Nikorag/Jellybox-Firmware/jellybox-firmware/JellyboxLogo.h

// Jellybox logo — 72x72 px, 9 bytes/row
static const uint8_t JELLYBOX_LOGO[] PROGMEM = {
  0x00, 0x00, 0x00, 0x00, 0x00, 0x00, 0x00, 0x00, 0x00,
  0x00, 0x00, 0x00, 0x00, 0x00, 0x00, 0x00, 0x00, 0x00,
  0x00, 0x00, 0x00, 0x00, 0x00, 0x00, 0x00, 0x00, 0x00,
  0x00, 0x00, 0x00, 0x00, 0x00, 0x00, 0x00, 0x00, 0x00,
  0x00, 0x00, 0x00, 0x00, 0x00, 0x00, 0x00, 0x00, 0x00,
  0x00, 0x00, 0x00, 0x00, 0x00, 0x00, 0x00, 0x00, 0x00,
  0x00, 0x00, 0x00, 0x00, 0x00, 0x00, 0x00, 0x00, 0x00,
  0x00, 0x00, 0x00, 0x00, 0x00, 0x00, 0x00, 0x00, 0x00,
  0x00, 0x00, 0x00, 0x00, 0x00, 0x00, 0x00, 0x00, 0x00,
  0x00, 0x00, 0x00, 0x00, 0x00, 0x00, 0x00, 0x00, 0x00,
  0x00, 0x00, 0x00, 0x00, 0x00, 0x00, 0x00, 0x00, 0x00,
  0x00, 0x00, 0x00, 0x00, 0x00, 0x00, 0x00, 0x00, 0x00,
  0x00, 0x00, 0x00, 0x00, 0x00, 0x00, 0x00, 0x00, 0x00,
  0x00, 0x00, 0x00, 0x00, 0x00, 0x00, 0x00, 0x00, 0x00,
  0x00, 0x00, 0x00, 0x00, 0x00, 0x00, 0x00, 0x00, 0x00,
  0x00, 0x00, 0x00, 0x00, 0xFF, 0x00, 0x00, 0x00, 0x00,
  0x00, 0x00, 0x00, 0x3F, 0xFF, 0xFC, 0x00, 0x00, 0x00,
  0x00, 0x00, 0x00, 0x63, 0xFF, 0xC6, 0x00, 0x00, 0x00,
  0x00, 0x00, 0x00, 0xC3, 0xFF, 0xC3, 0x00, 0x00, 0x00,
  0x00, 0x00, 0x01, 0x9C, 0x3C, 0x39, 0x80, 0x00, 0x00,
  0x00, 0x00, 0x01, 0x38, 0x7E, 0x1C, 0x80, 0x00, 0x00,
  0x00, 0x00, 0x03, 0x31, 0xC3, 0x8C, 0xC0, 0x00, 0x00,
  0x00, 0x00, 0x02, 0x73, 0x81, 0xCE, 0x40, 0x00, 0x00,
  0x00, 0x00, 0x02, 0x67, 0x9E, 0xE6, 0x40, 0x00, 0x00,
  0x00, 0x00, 0x06, 0xE7, 0x3F, 0xE7, 0x60, 0x00, 0x00,
  0x00, 0x00, 0xFC, 0xE7, 0x3F, 0xE7, 0x3F, 0x00, 0x00,
  0x00, 0x03, 0xED, 0xCF, 0x3F, 0xF7, 0xB7, 0xC0, 0x00,
  0x00, 0x07, 0x0D, 0xCF, 0xFF, 0xF3, 0xB0, 0xE0, 0x00,
  0x00, 0x0F, 0xC9, 0xCF, 0xFF, 0xF3, 0x93, 0xF0, 0x00,
  0x00, 0x0C, 0x79, 0xDF, 0x7F, 0xFB, 0x9E, 0x30, 0x00,
  0x00, 0x18, 0x3F, 0xDF, 0xFF, 0xFB, 0xF8, 0x18, 0x00,
  0x00, 0x18, 0x0F, 0x9F, 0xFF, 0xF9, 0xF0, 0x18, 0x00,
  0x00, 0x30, 0x03, 0xFF, 0xFF, 0xFF, 0xC0, 0x0C, 0x00,
  0x00, 0x20, 0x00, 0xFF, 0xFF, 0xFF, 0x00, 0x0C, 0x00,
  0x00, 0x60, 0x00, 0x3F, 0xFF, 0xFC, 0x00, 0x06, 0x00,
  0x00, 0x60, 0x00, 0x0F, 0xFF, 0xF0, 0x00, 0x06, 0x00,
  0x00, 0x70, 0x00, 0x03, 0xFF, 0xC0, 0x00, 0x0E, 0x00,
  0x00, 0x38, 0x00, 0x00, 0xFF, 0x00, 0x00, 0x3C, 0x00,
  0x00, 0x0E, 0x00, 0x00, 0x7E, 0x00, 0x00, 0x70, 0x00,
  0x00, 0x07, 0x80, 0x00, 0x7E, 0x00, 0x01, 0xE0, 0x00,
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
};
#define JELLYBOX_LOGO_W 72
#define JELLYBOX_LOGO_H 72
